mamollica42/Nissan_Leaf_Driving_Simulation_Repo/Documentation/Images/PowerSupply.jpg

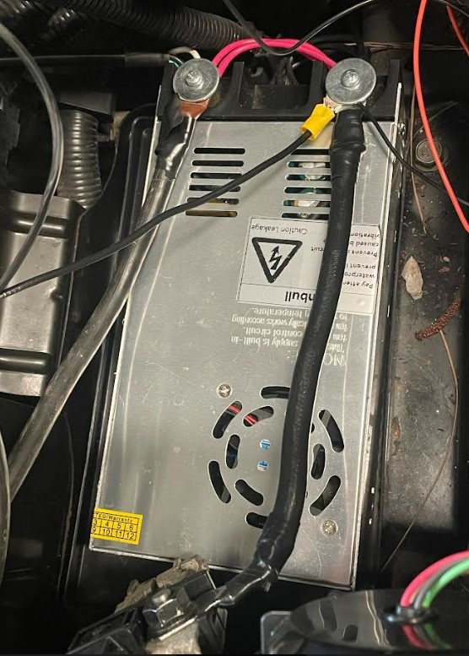
Documentation/Images/PowerSupply.jpg
