mamollica42/Nissan_Leaf_Driving_Simulation_Repo/Documentation/3D Models/Steering/Adapter Plate.stl

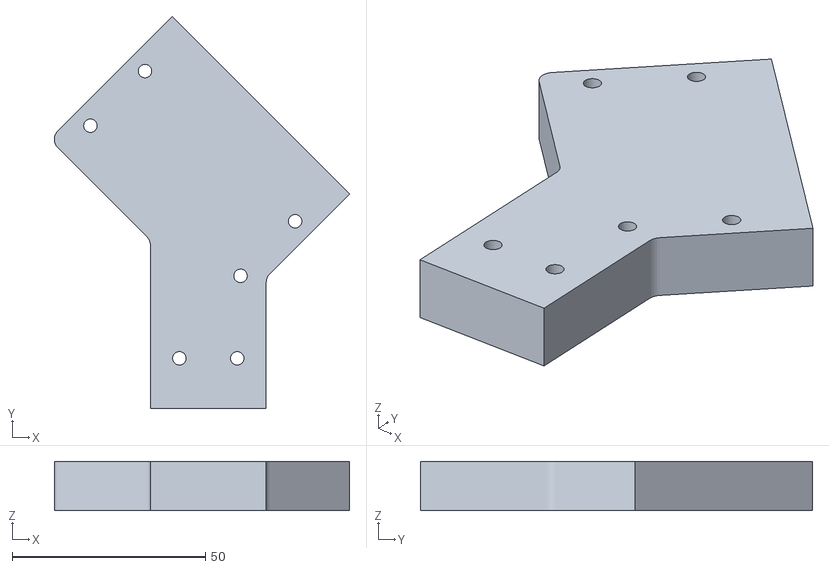
[picture p102: CAD file, 2023-04-30]
Documentation/3D Models/Steering/Adapter Plate.stl
76.5 x 101.5 x 12.7
