mamollica42/Nissan_Leaf_Driving_Simulation_Repo/Documentation/Electrical/Schematics/Steering_Schematic.pdf

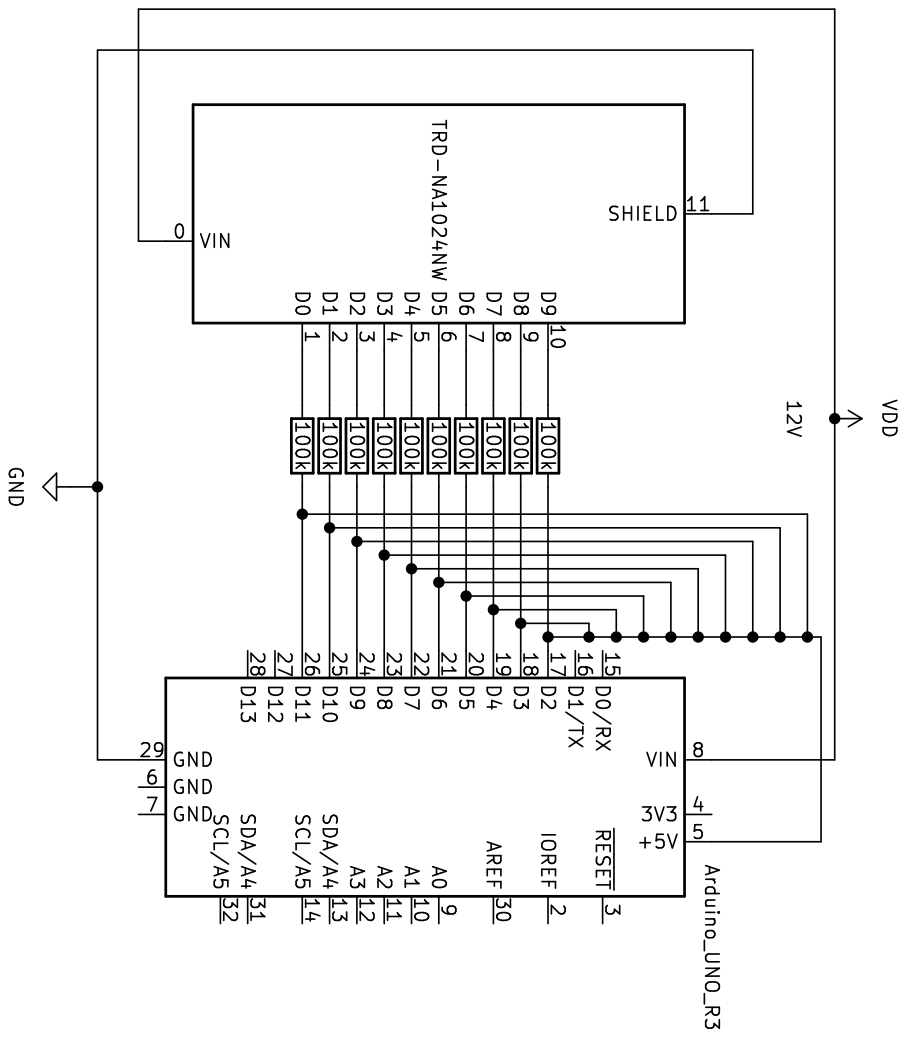
[picture p109: page 1]
