mamollica42/Nissan_Leaf_Driving_Simulation_Repo/Documentation/Electrical/Schematics/PowerSystem.pdf

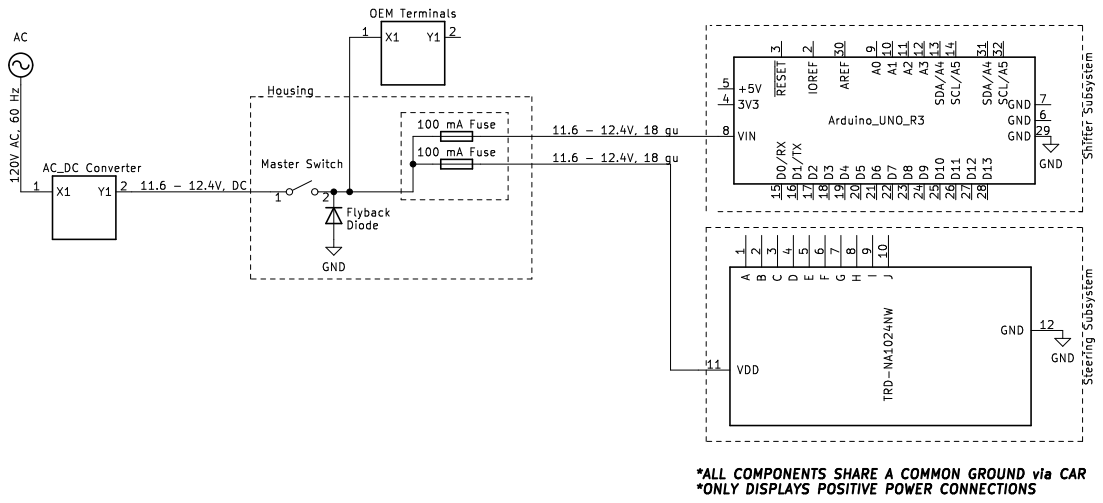
[picture p110: page 1]
