mamollica42/Nissan_Leaf_Driving_Simulation_Repo/Documentation/Electrical/Schematics/ShifterSpice.asc

D1: zener; MYD
R1: res; 1000
V1: voltage; 15
Named nets: 0
.model MYD ako: BZX84B8V2L Bv=5.1
.tran 0.1
