mamollica42/Nissan_Leaf_Driving_Simulation_Repo/Documentation/Electrical/Schematics/autolight.kicad_sch

## KiCad design Documentation/Electrical/Schematics/autolight.kicad_sch (2023-04-30)

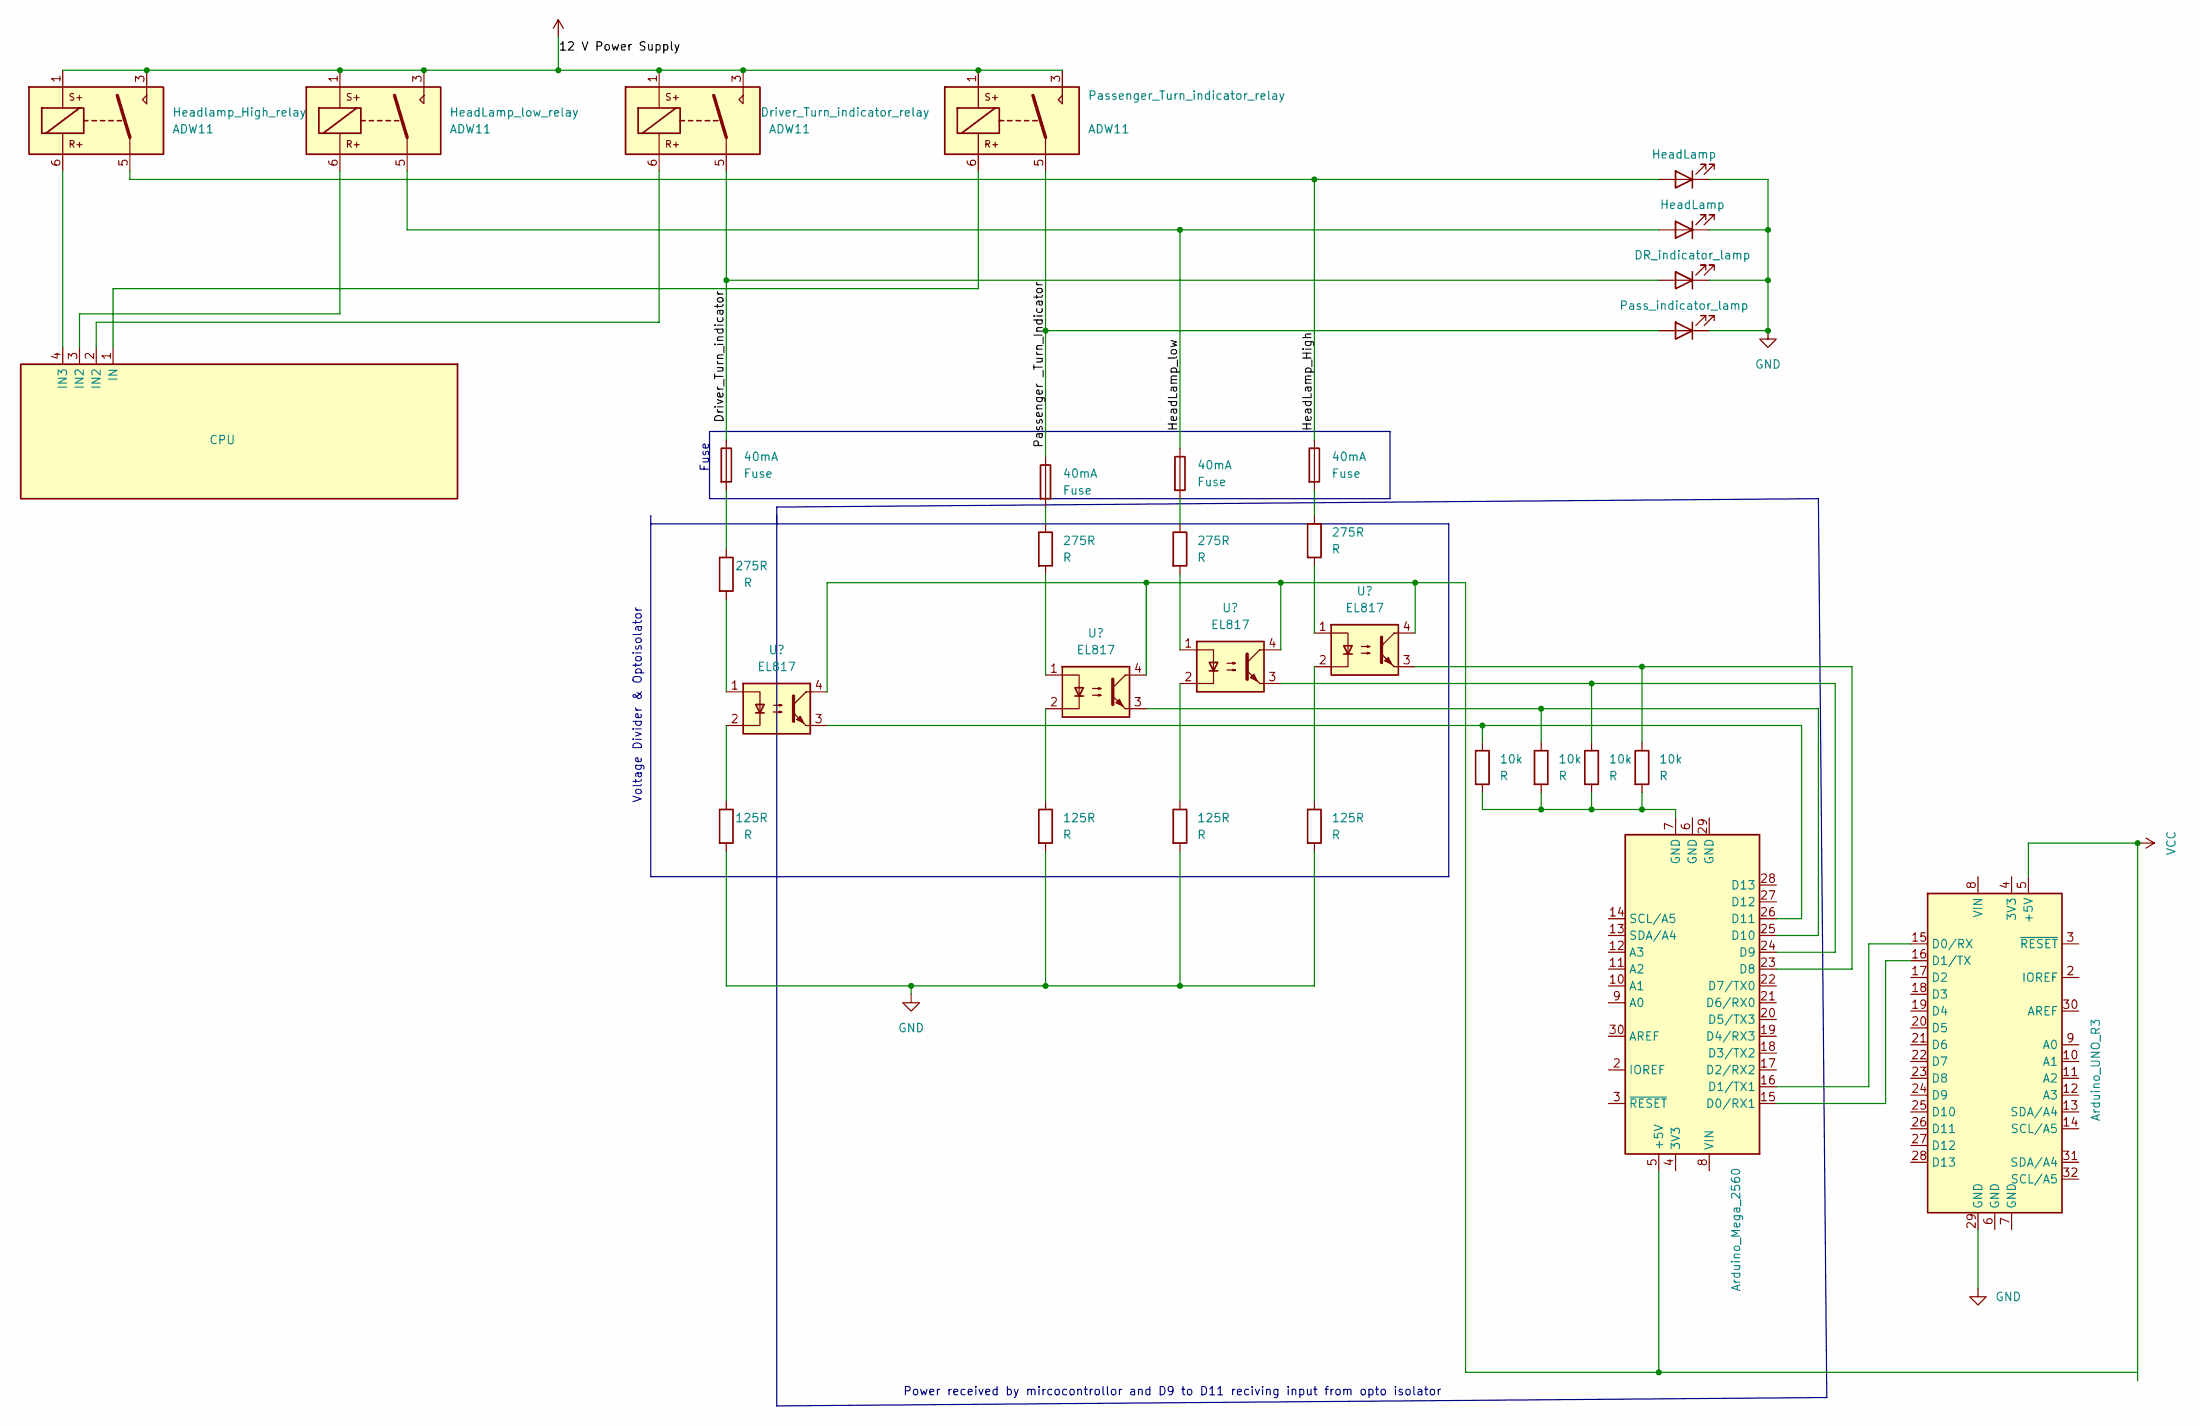
[picture p111: schematic autolight.kicad_sch]

Parts:
10k, 125R, 275R: R
40mA: Fuse
DR_indicator_lamp: LED
Driver_Turn_indicator_relay: ADW11; Relay_1P1T_NO_10x24x18.8mm_Panasonic_ADW11xxxxW_THT
HeadLamp: LED
HeadLamp_low_relay: ADW11; Relay_1P1T_NO_10x24x18.8mm_Panasonic_ADW11xxxxW_THT
Headlamp_High_relay: ADW11; Relay_1P1T_NO_10x24x18.8mm_Panasonic_ADW11xxxxW_THT
Pass_indicator_lamp: LED
Passenger_Turn_indicator_relay: ADW11; Relay_1P1T_NO_10x24x18.8mm_Panasonic_ADW11xxxxW_THT

Connections:
Driver_Turn_indicator: 40mA.1, DR_indicator_lamp.2 (A), Driver_Turn_indicator_relay.5
HeadLamp_High: 40mA.1, HeadLamp.2 (A), Headlamp_High_relay.5
HeadLamp_low: 40mA.1, HeadLamp.2 (A), HeadLamp_low_relay.5
unnamed: 40mA.2, 275R.1
unnamed: DR_indicator_lamp.1 (K), HeadLamp.1 (K), Pass_indicator_lamp.1 (K)
Passenger _Turn_Indicator: 40mA.1, Pass_indicator_lamp.2 (A), Passenger_Turn_indicator_relay.5
V Power Supply: Driver_Turn_indicator_relay.1, Driver_Turn_indicator_relay.3, HeadLamp_low_relay.1, HeadLamp_low_relay.3, Headlamp_High_relay.1, Headlamp_High_relay.3, Passenger_Turn_indicator_relay.1, Passenger_Turn_indicator_relay.3

Notes on the sheet:
Fuse
Power received by mircocontrollor and D9 to D11 reciving input from opto isolator
Voltage Divider & Optoisolator
